makethingshappy/IoTextra-Digital/Input/v.3.02/media/01_-_IoTextra_Input_3D_view.png

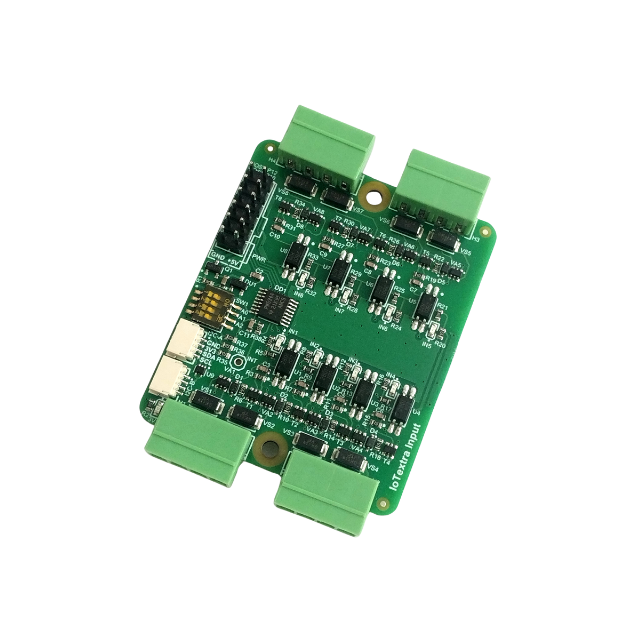
Input/v.3.02/media/01_-_IoTextra_Input_3D_view.png
