makethingshappy/IoTextra-Digital/Input/v.3.02/media/02_-_IoTextra_Input_with_and_without_Qwiic_connector.png

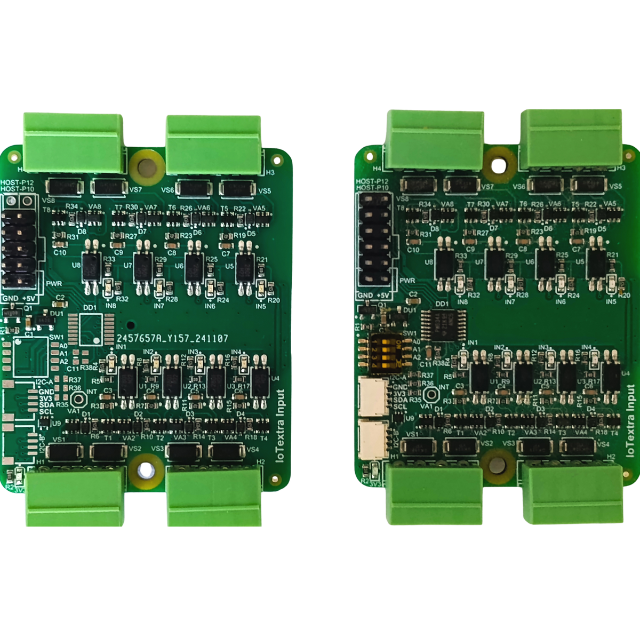
Input/v.3.02/media/02_-_IoTextra_Input_with_and_without_Qwiic_connector.png
