makethingshappy/IoTextra-Digital/Input/v.3.02/media/03_-_IoTextra_Input_TOP_view.png

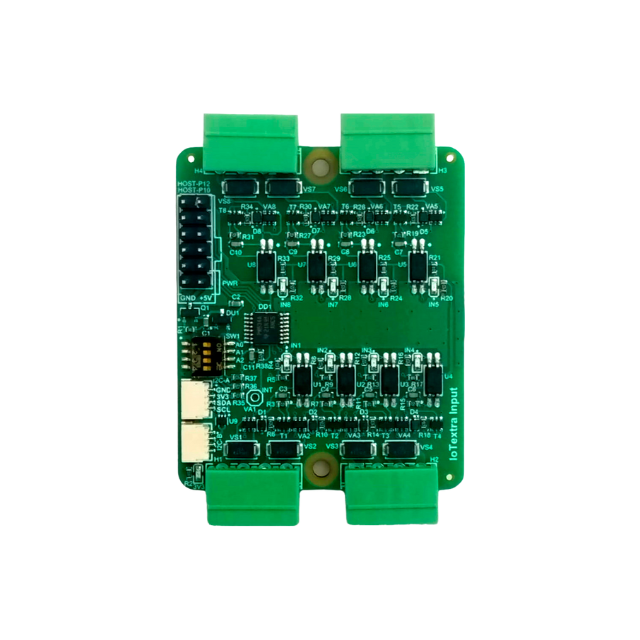
Input/v.3.02/media/03_-_IoTextra_Input_TOP_view.png
