makethingshappy/IoTextra-Digital/Input/v.3.02/media/04_-_IoTextra_Input_BOTTOM_view.png

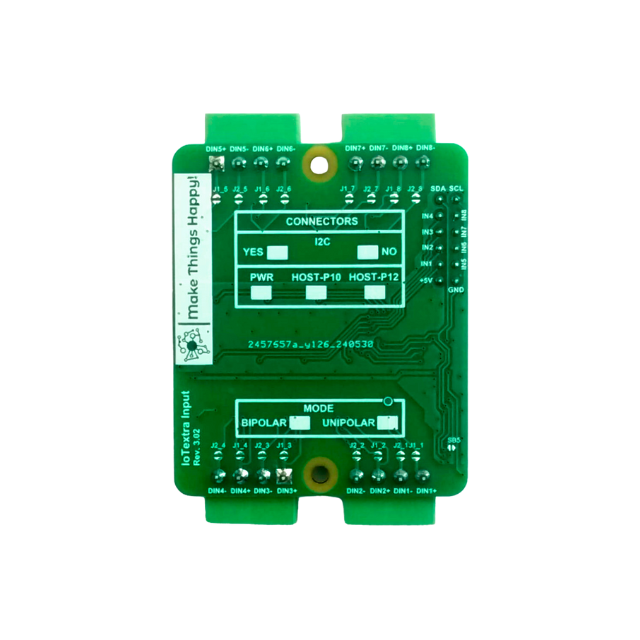
Input/v.3.02/media/04_-_IoTextra_Input_BOTTOM_view.png
