makethingshappy/IoTextra-Digital/Input/v.3.02/media/05_-_IoTextra_Input_HOST_connector_pinout.png

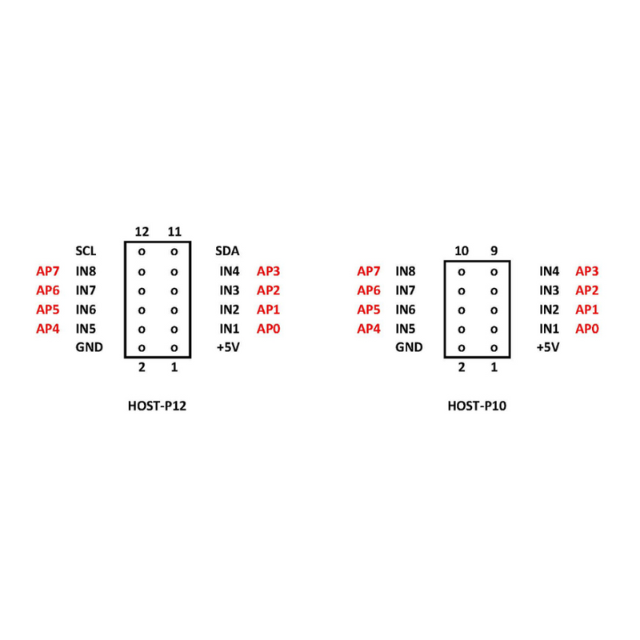
Input/v.3.02/media/05_-_IoTextra_Input_HOST_connector_pinout.png
