makethingshappy/IoTextra-Digital/Input/v.3.02/media/06_-_IoTsmart_RP2040_and_IoTextra_Input.png

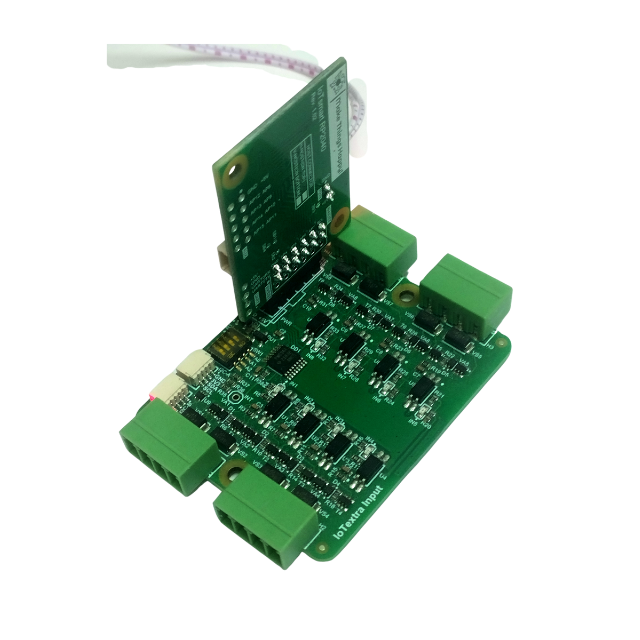
Input/v.3.02/media/06_-_IoTsmart_RP2040_and_IoTextra_Input.png
