makethingshappy/IoTextra-Digital/Input/v.3.02/media/07_-_IoTsmart_RP2350_and_IoTextra_Input.png

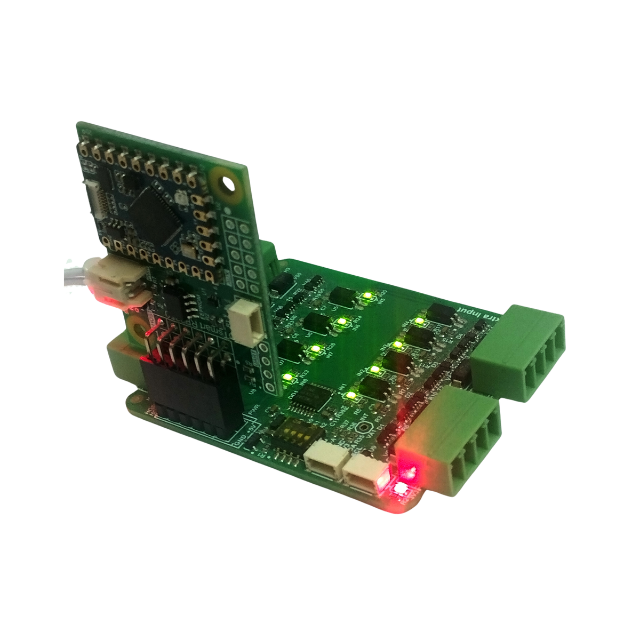
Input/v.3.02/media/07_-_IoTsmart_RP2350_and_IoTextra_Input.png
