makethingshappy/IoTextra-Digital/Input/v.3.02/media/12_-_IoTbase_PICO_and_IoTextra_Input_with_Raspberry_PICO2.png

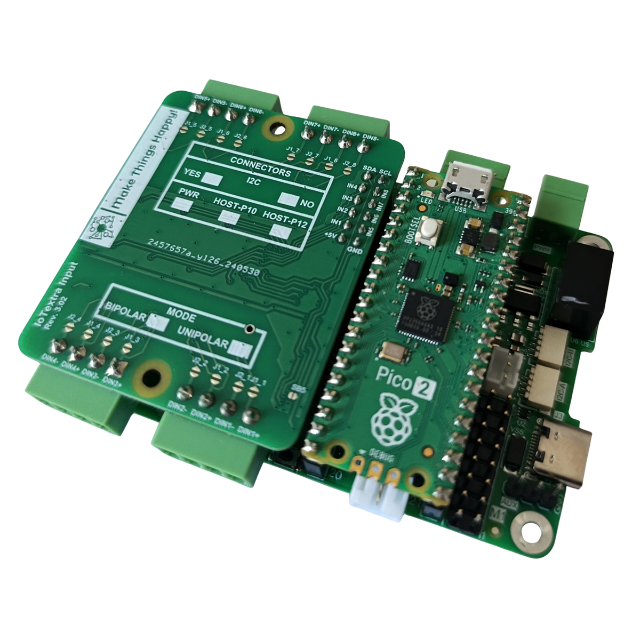
Input/v.3.02/media/12_-_IoTbase_PICO_and_IoTextra_Input_with_Raspberry_PICO2.png
