makethingshappy/IoTextra-Digital/Input/v.3.02/media/13_-_IoTextra_Input_and_IoTbase_PICO_with_RP2040_Plus.png

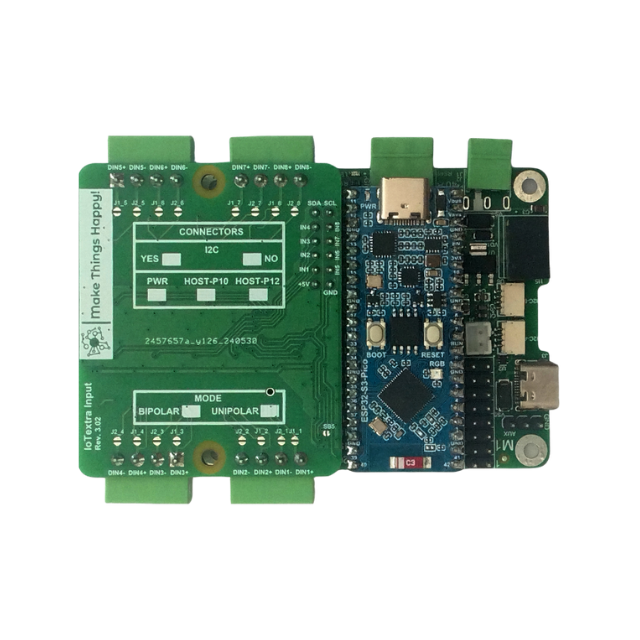
Input/v.3.02/media/13_-_IoTextra_Input_and_IoTbase_PICO_with_RP2040_Plus.png
