makethingshappy/IoTextra-Digital/Input/v.3.02/media/15_-_IoTextra_Input_and_Raspberry_Pi_Zero.png

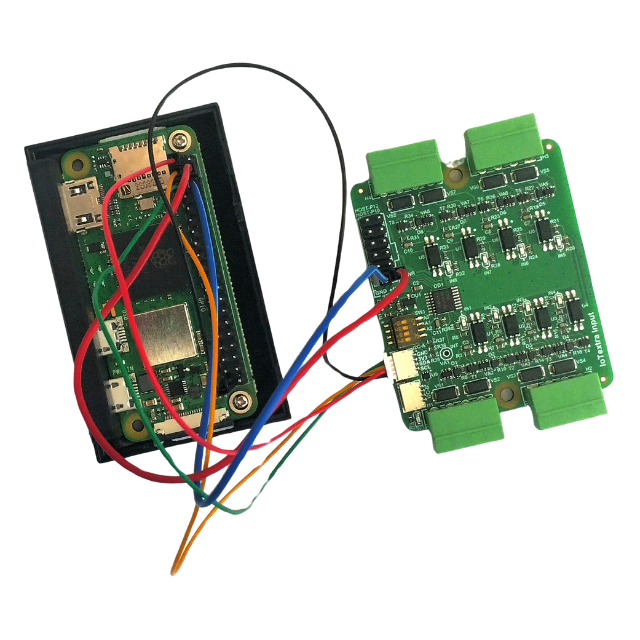
Input/v.3.02/media/15_-_IoTextra_Input_and_Raspberry_Pi_Zero.png
