makethingshappy/IoTextra-Digital/Input/v.3.02/media/16_-_IoTextra_Input_and_Feather_Adaptor_with_Proton2.png

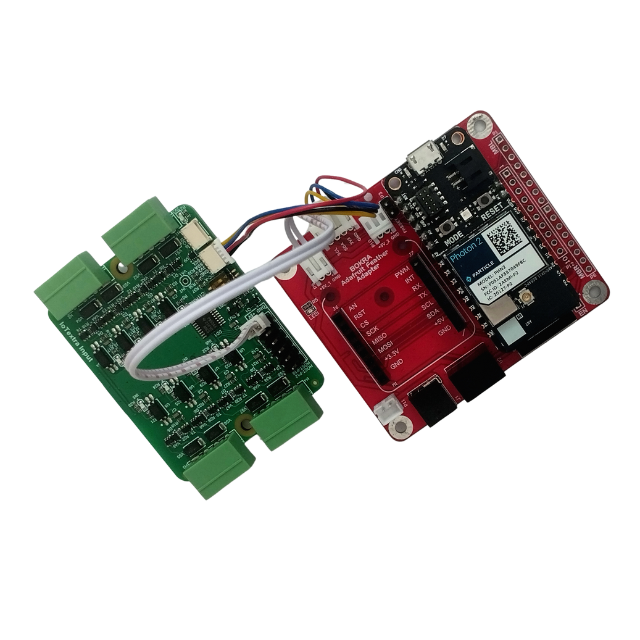
Input/v.3.02/media/16_-_IoTextra_Input_and_Feather_Adaptor_with_Proton2.png
