makethingshappy/IoTextra-Digital/MOSFET2/v.3.02/media/01 - IoTextra MOSFET2 and IoTsmart ESP32-S3 .png

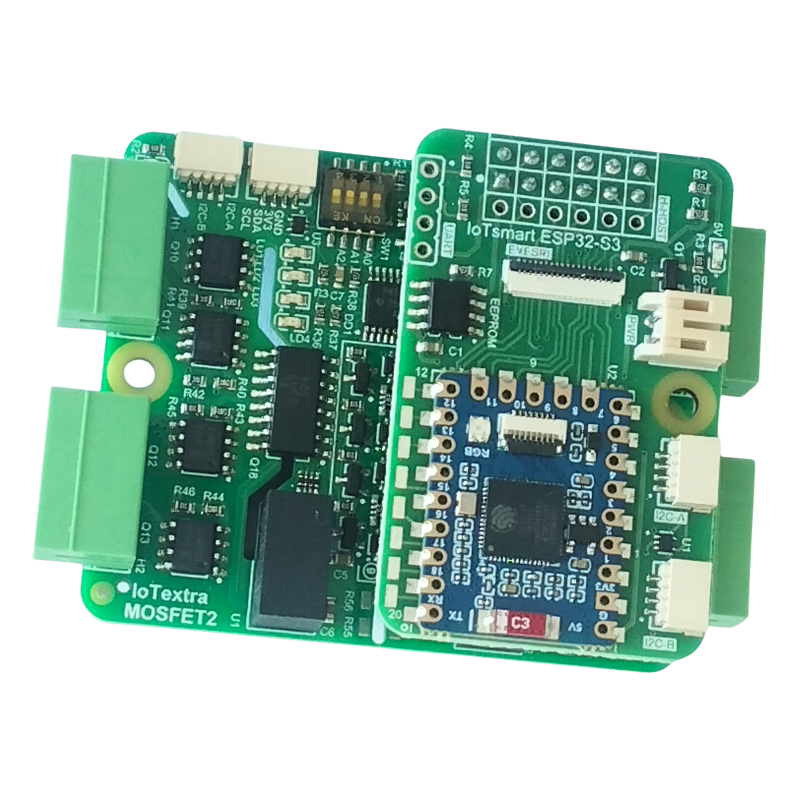
MOSFET2/v.3.02/media/01 - IoTextra MOSFET2 and IoTsmart ESP32-S3 .png
