makethingshappy/IoTextra-Digital/MOSFET2/v.3.02/media/02 - IoTextra MOSFET2 TOP view.png

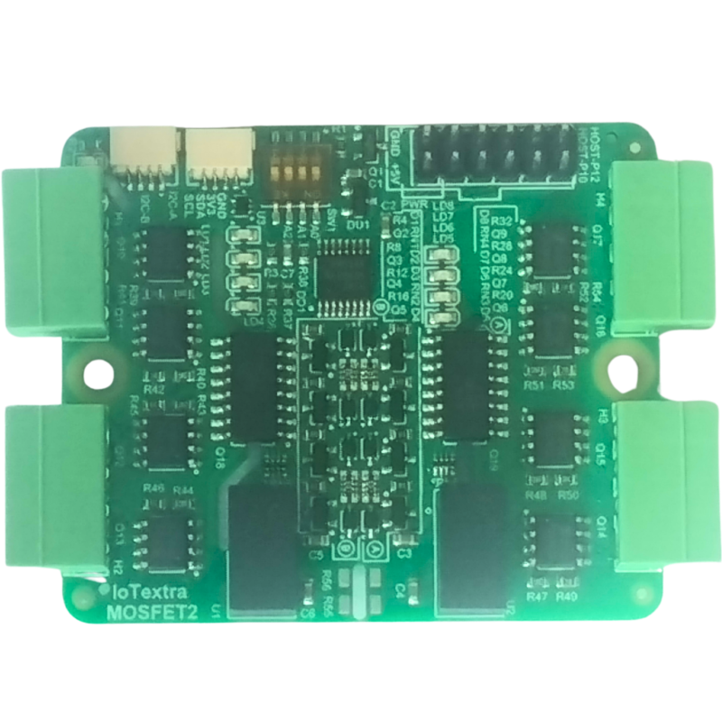
MOSFET2/v.3.02/media/02 - IoTextra MOSFET2 TOP view.png
