makethingshappy/IoTextra-Digital/MOSFET2/v.3.02/media/05 - IoTextra MOSFET2 and IoTsmart RP2350A.png

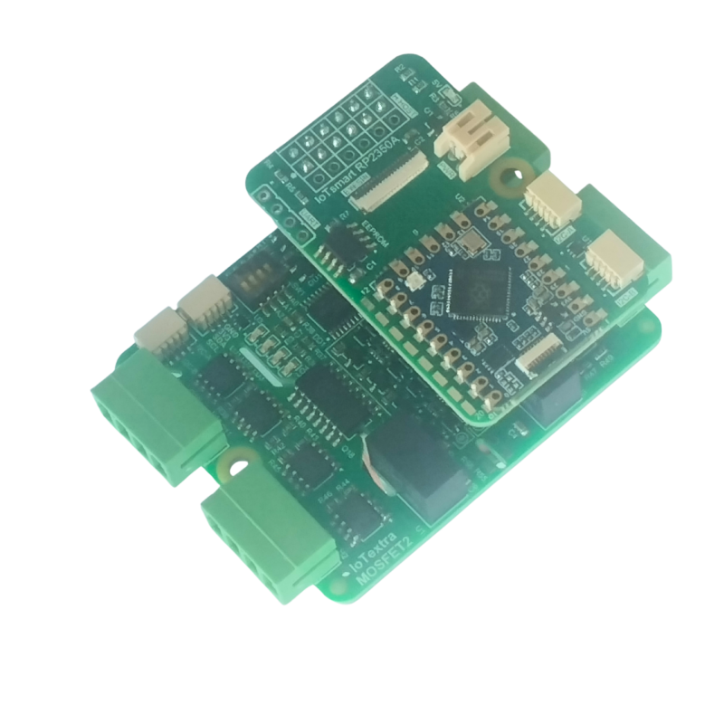
MOSFET2/v.3.02/media/05 - IoTextra MOSFET2 and IoTsmart RP2350A.png
