makethingshappy/IoTextra-Digital/MOSFET2/v.3.02/media/07 - IoTextra MOSFET2 and IoTsmart XIAO with XIAO ESP32-C6.png

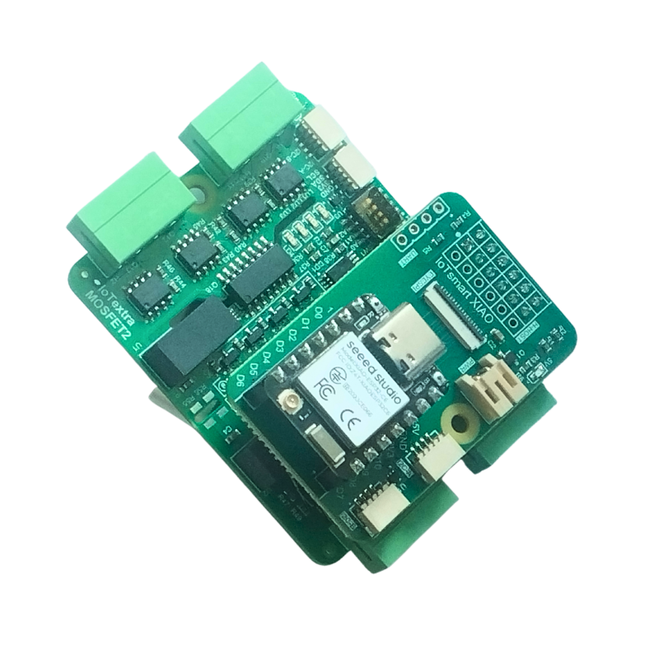
MOSFET2/v.3.02/media/07 - IoTextra MOSFET2 and IoTsmart XIAO with XIAO ESP32-C6.png
