makethingshappy/IoTextra-Digital/MOSFET2/v.3.02/media/08 - IoTextra MOSFET2 and IoTbase Feather with Proton2.png

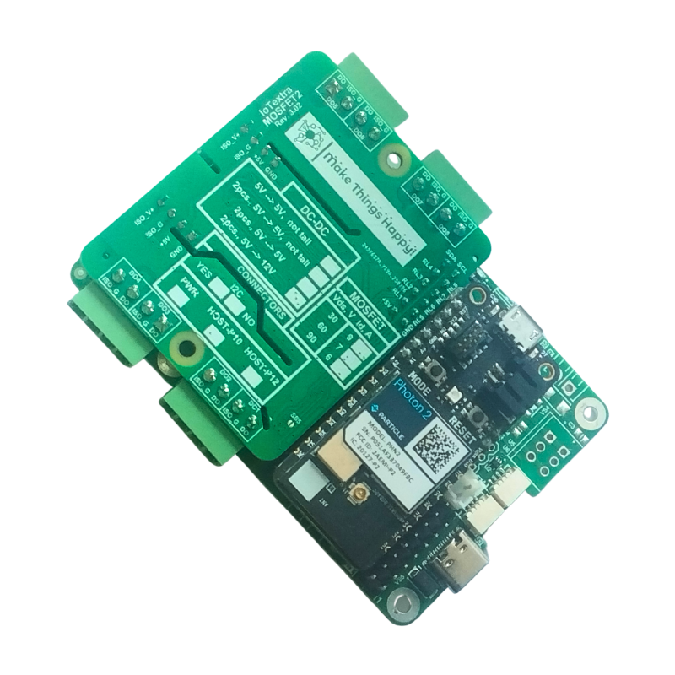
MOSFET2/v.3.02/media/08 - IoTextra MOSFET2 and IoTbase Feather with Proton2.png
