makethingshappy/IoTextra-Digital/Octal3/v.3.02/media/01 - IoTextra Octal3 - 3D view.png

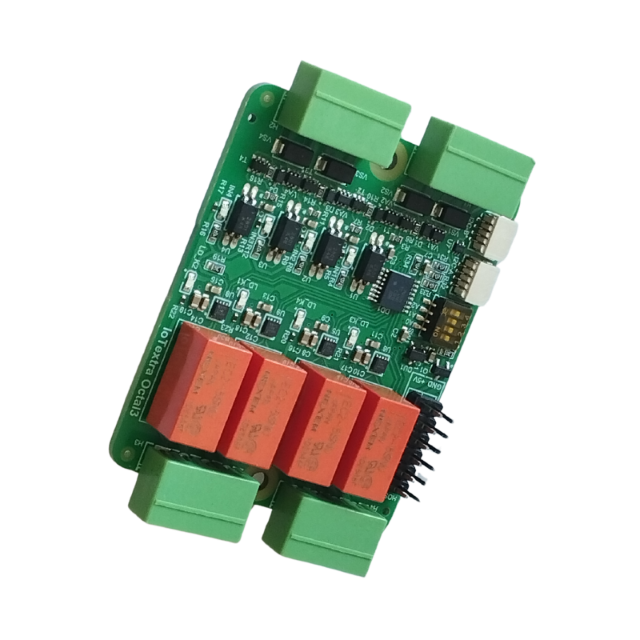
Octal3/v.3.02/media/01 - IoTextra Octal3 - 3D view.png
