makethingshappy/IoTextra-Digital/Octal3/v.3.02/media/02 - IoTextra Octal3 - TOP.png

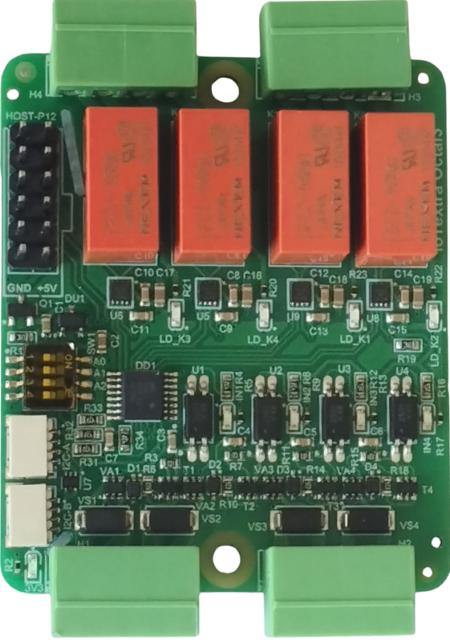
Octal3/v.3.02/media/02 - IoTextra Octal3 - TOP.png
