makethingshappy/IoTextra-Digital/Octal3/v.3.02/media/03 - IoTextra Octal3 - BOTTOM view.png

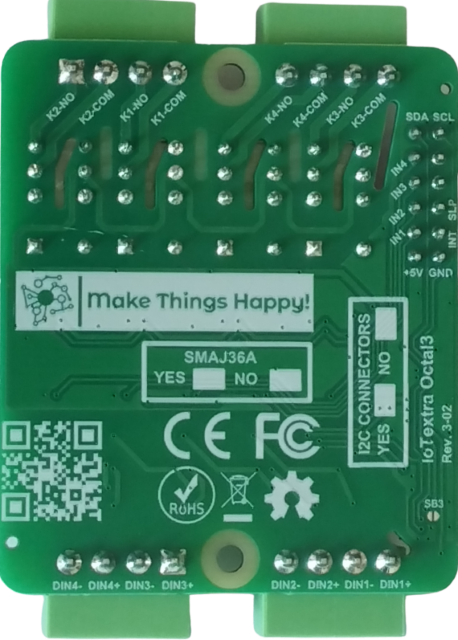
Octal3/v.3.02/media/03 - IoTextra Octal3 - BOTTOM view.png
