makethingshappy/IoTextra-Digital/Octal3/v.3.02/media/04 - HOST.jpg

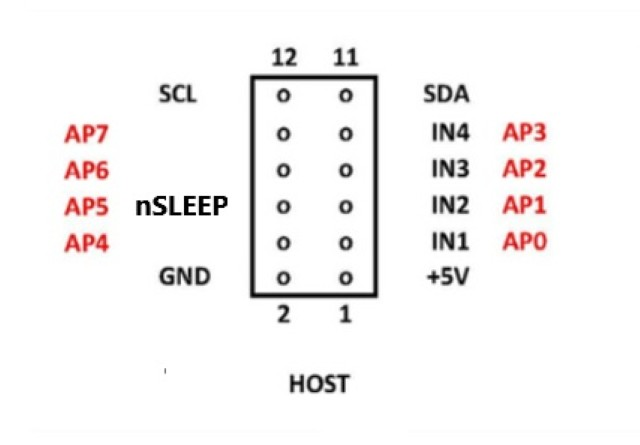
Octal3/v.3.02/media/04 - HOST.jpg
