makethingshappy/IoTextra-Digital/Octal3/v.3.02/media/05 - IoTextra Octal3 and IoTsmart RP2040 .png

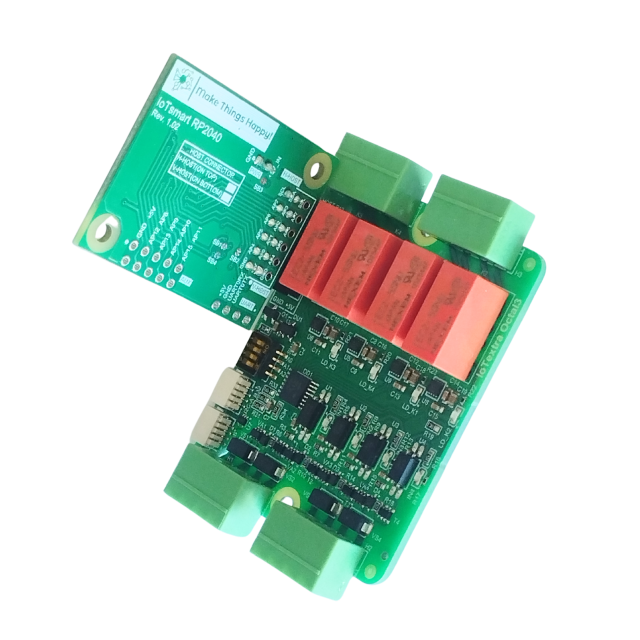
Octal3/v.3.02/media/05 - IoTextra Octal3 and IoTsmart RP2040 .png
