makethingshappy/IoTextra-Digital/Octal3/v.3.02/media/06 - IoTextra Octal3 and IoTsmart RP2350A 2-01 .png

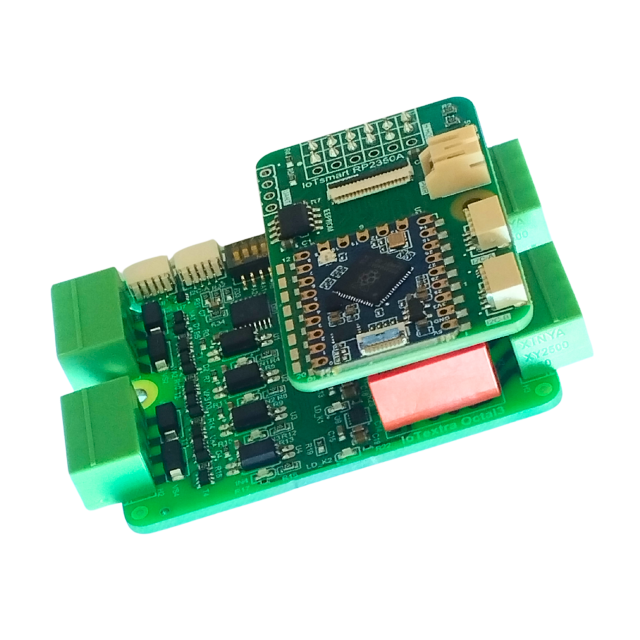
Octal3/v.3.02/media/06 - IoTextra Octal3 and IoTsmart RP2350A 2-01 .png
