makethingshappy/IoTextra-Digital/Octal3/v.3.02/media/07 - IoTextra Octal3 and IoTsmart RP2350 1-02 .png

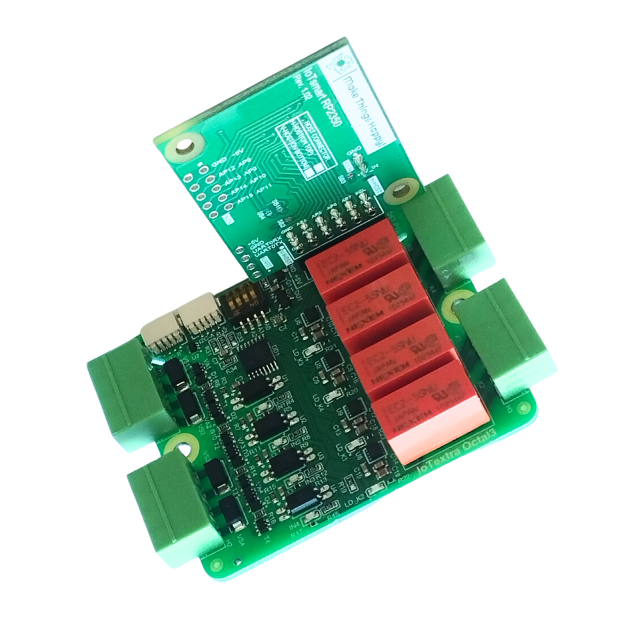
Octal3/v.3.02/media/07 - IoTextra Octal3 and IoTsmart RP2350 1-02 .png
