makethingshappy/IoTextra-Digital/Octal3/v.3.02/media/08 - IoTextra Octal3 and IoTsmart ESP32-S3 2-01 - 1.png

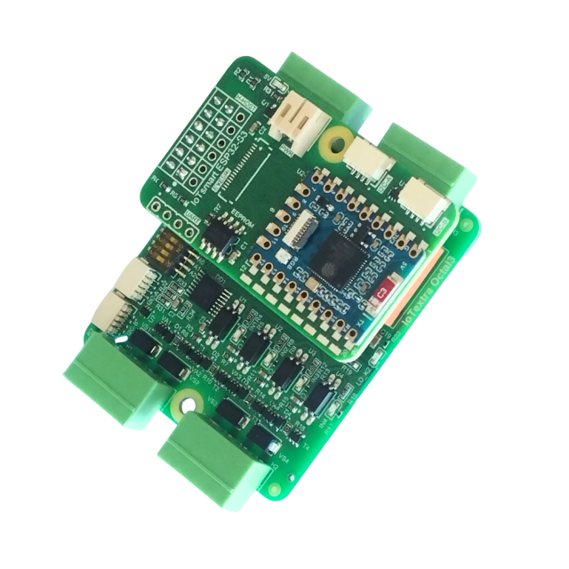
Octal3/v.3.02/media/08 - IoTextra Octal3 and IoTsmart ESP32-S3 2-01 - 1.png
