makethingshappy/IoTextra-Digital/Octal3/v.3.02/media/10 - IoTextra Octal3 and IoTsmart ESP32-S3 1-02.png

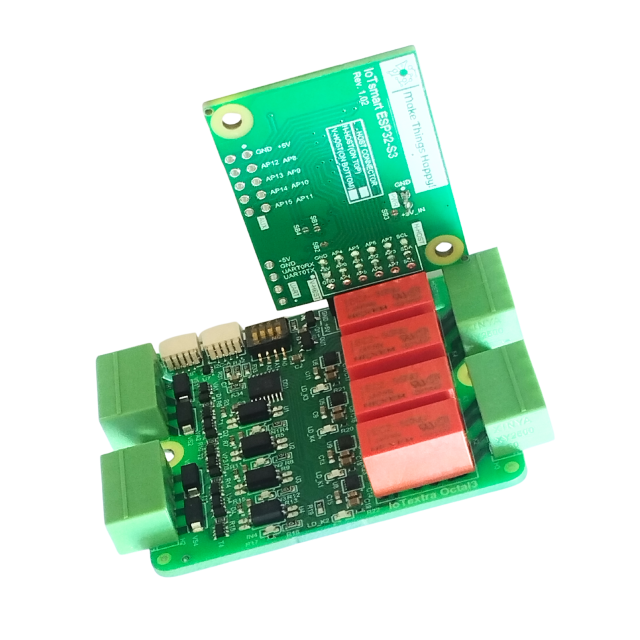
Octal3/v.3.02/media/10 - IoTextra Octal3 and IoTsmart ESP32-S3 1-02.png
