makethingshappy/IoTextra-Digital/Octal/v.3.04/media/02 - IoTextra Octal TOP view.png

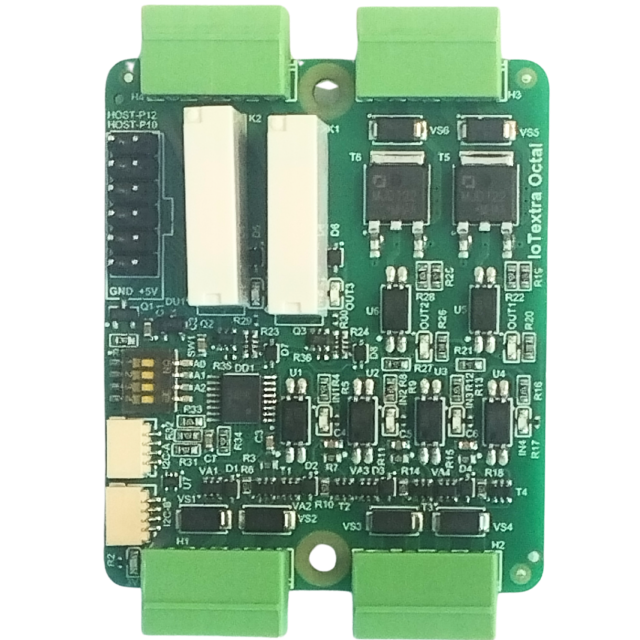
Octal/v.3.04/media/02 - IoTextra Octal TOP view.png
