makethingshappy/IoTextra-Digital/Octal/v.3.04/media/03 - IoTextra Octal BOTTOM view.png

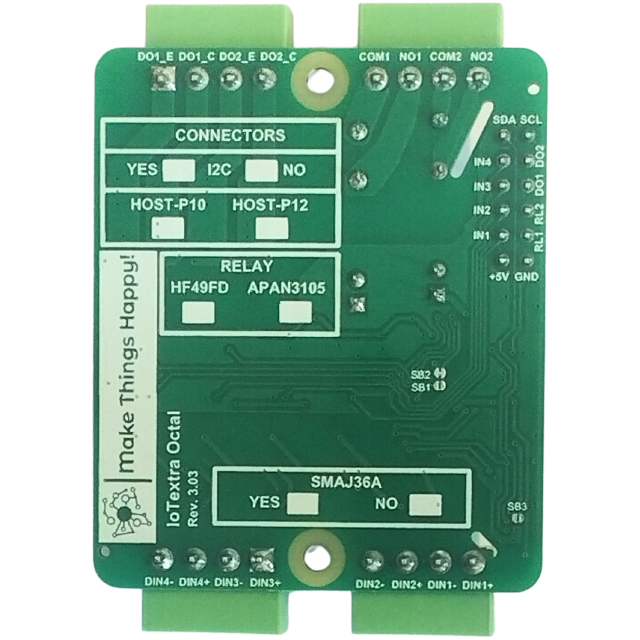
Octal/v.3.04/media/03 - IoTextra Octal BOTTOM view.png
