makethingshappy/IoTextra-Digital/Octal/v.3.04/media/05 - IoTextra Octal and IoTsmart RP2040 1-02.png

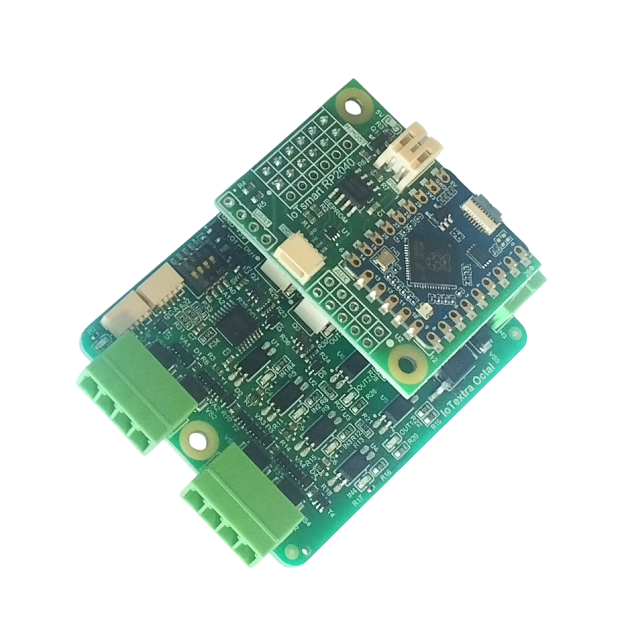
Octal/v.3.04/media/05 - IoTextra Octal and IoTsmart RP2040 1-02.png
