makethingshappy/IoTextra-Digital/Octal/v.3.04/media/06 - IoTextra Octal and IoTsmart RP2350 1-02 - 1.png

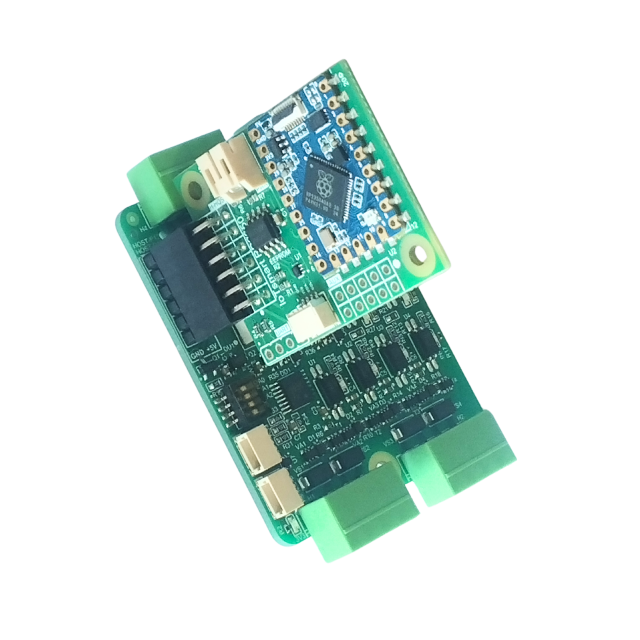
Octal/v.3.04/media/06 - IoTextra Octal and IoTsmart RP2350 1-02 - 1.png
