makethingshappy/IoTextra-Digital/Octal/v.3.04/media/07 - IoTextra Octal and IoTsmart RP2350 1-02 - 2.png

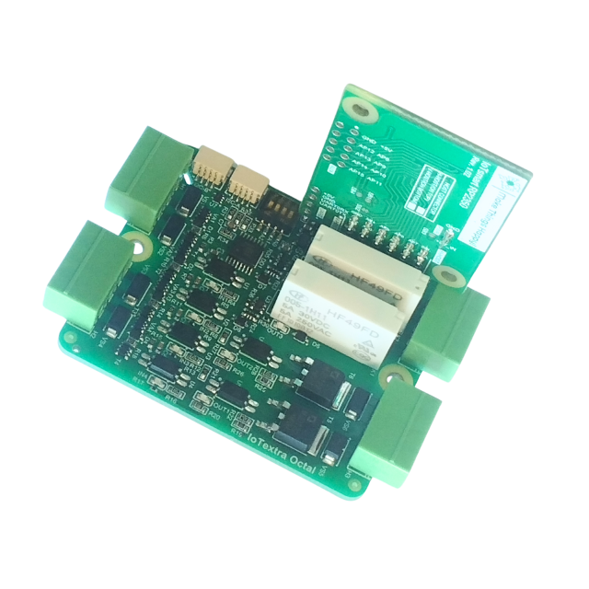
Octal/v.3.04/media/07 - IoTextra Octal and IoTsmart RP2350 1-02 - 2.png
