makethingshappy/IoTextra-Digital/Octal/v.3.04/media/08 - IoTextra Octal and IoTsmart RP2350 2-01 A.png

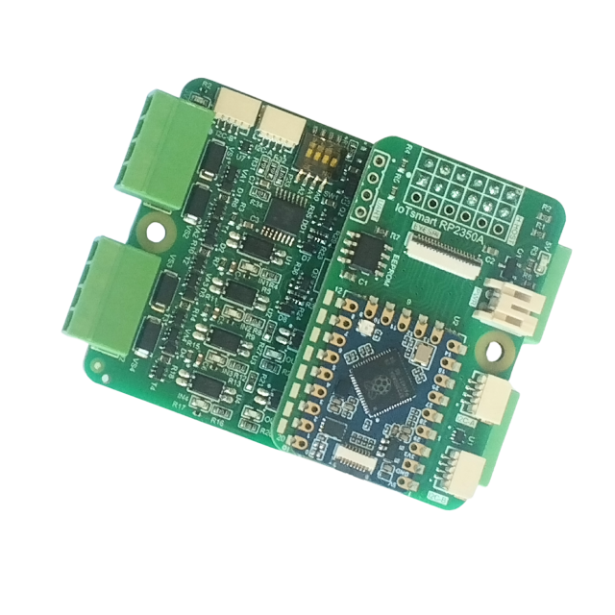
Octal/v.3.04/media/08 - IoTextra Octal and IoTsmart RP2350 2-01 A.png
