makethingshappy/IoTextra-Digital/Octal/v.3.04/media/10 - IoTextra Octal and IoTbase PICO with PICO2.png

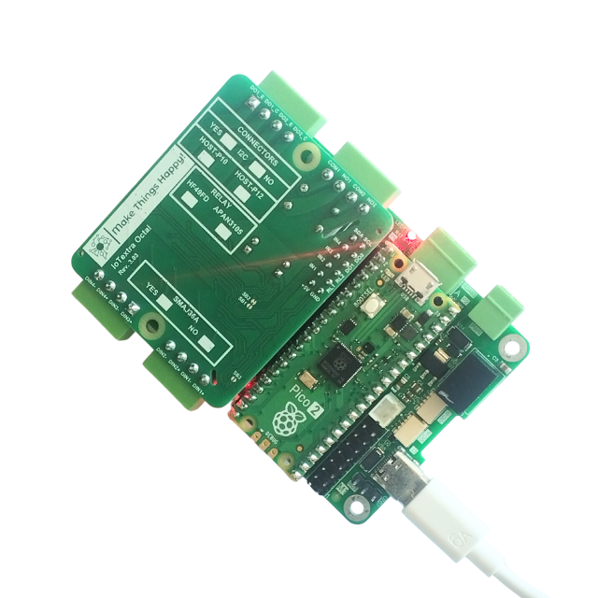
Octal/v.3.04/media/10 - IoTextra Octal and IoTbase PICO with PICO2.png
