makethingshappy/IoTextra-Digital/Octal/v.3.04/media/11 - IoTextra Octal and IoTbase PICO with Waveshare ESP32-S3-Pico.png

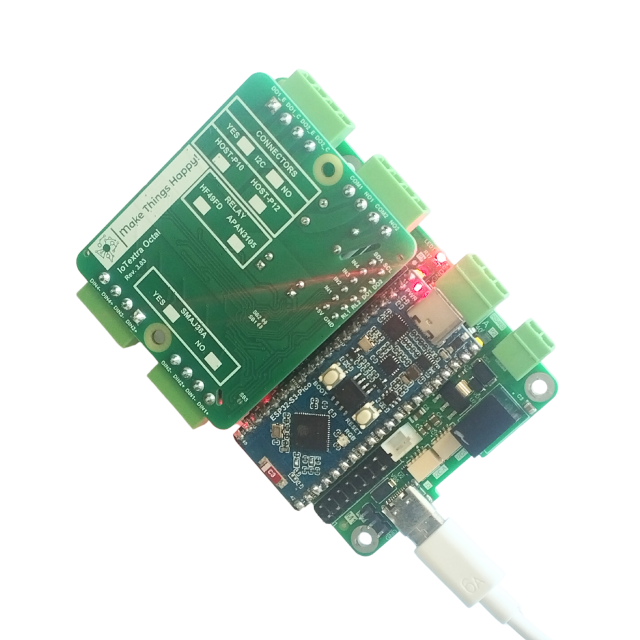
Octal/v.3.04/media/11 - IoTextra Octal and IoTbase PICO with Waveshare ESP32-S3-Pico.png
