makethingshappy/IoTextra-Digital/Octal/v.3.04/media/12 - IoTextra Octal and IoTbase NANO with Waveshare ESP32-S3-NANO.png

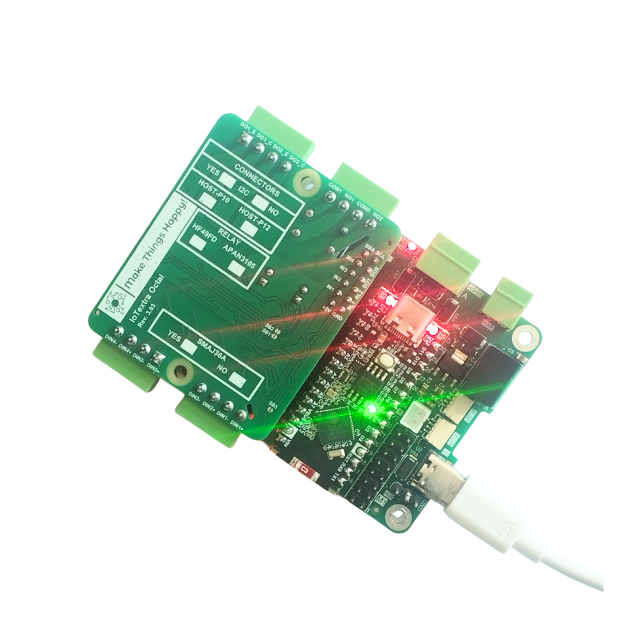
Octal/v.3.04/media/12 - IoTextra Octal and IoTbase NANO with Waveshare ESP32-S3-NANO.png
