makethingshappy/IoTextra-Digital/Relay2/v3.02/media/02_-_IoTextra_Relay2_with_and_without_Qwiic_connector.png

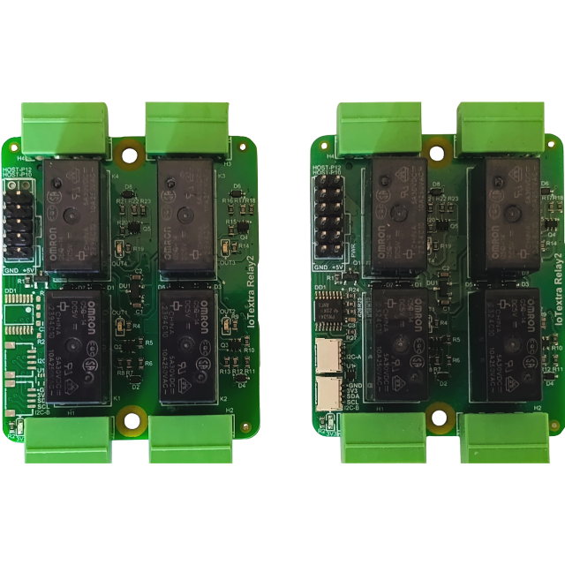
Relay2/v3.02/media/02_-_IoTextra_Relay2_with_and_without_Qwiic_connector.png
