makethingshappy/IoTextra-Digital/Relay2/v3.02/media/04_-_IoTextra_Relay2_BOTTOM_view.png

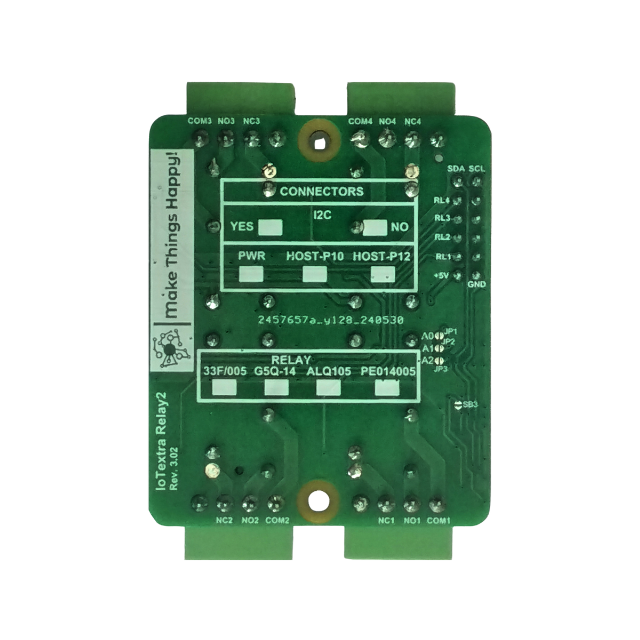
Relay2/v3.02/media/04_-_IoTextra_Relay2_BOTTOM_view.png
