makethingshappy/IoTextra-Digital/Relay2/v3.02/media/06_-_IoTsmart_RP2040_and_IoTextra_Relay2_-_1.png

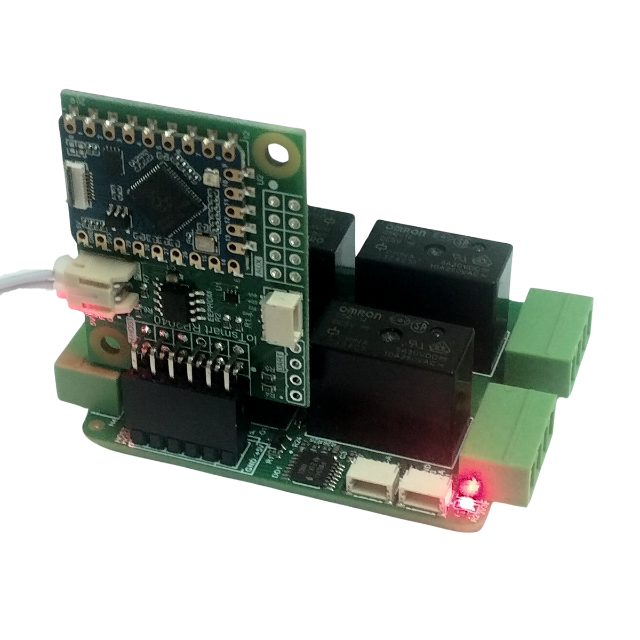
Relay2/v3.02/media/06_-_IoTsmart_RP2040_and_IoTextra_Relay2_-_1.png
