makethingshappy/IoTextra-Digital/Relay2/v3.02/media/11_-_IoTextra_Relay2_and_Raspberry_Pi_Zero.png

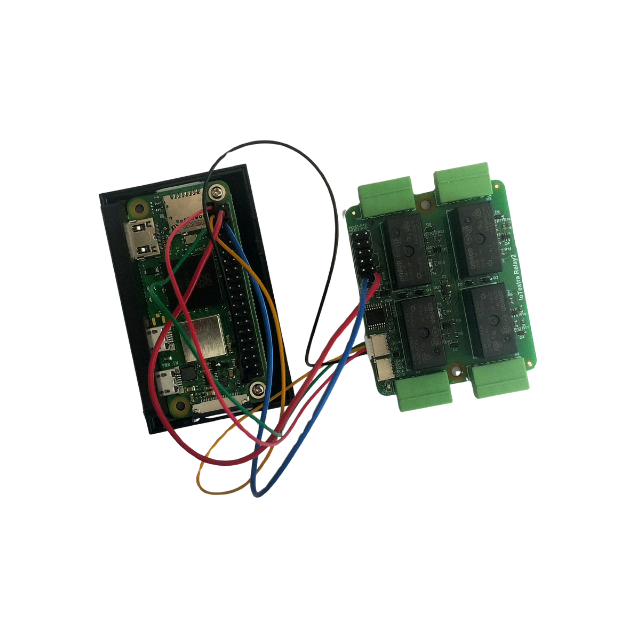
Relay2/v3.02/media/11_-_IoTextra_Relay2_and_Raspberry_Pi_Zero.png
