makethingshappy/IoTextra-Digital/Relay2/v3.02/media/12_-_IoTexra_Relay2_and_Feather_Adaptor_with_Proton2.png

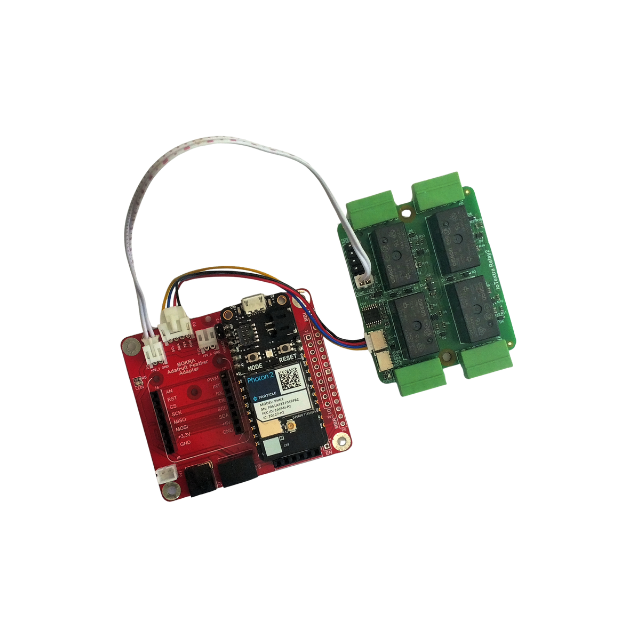
Relay2/v3.02/media/12_-_IoTexra_Relay2_and_Feather_Adaptor_with_Proton2.png
