makethingshappy/IoTextra-Digital/SSR Small/v.3.02/media/03_-_IoTextra_SSR_Small_TOP_view.png

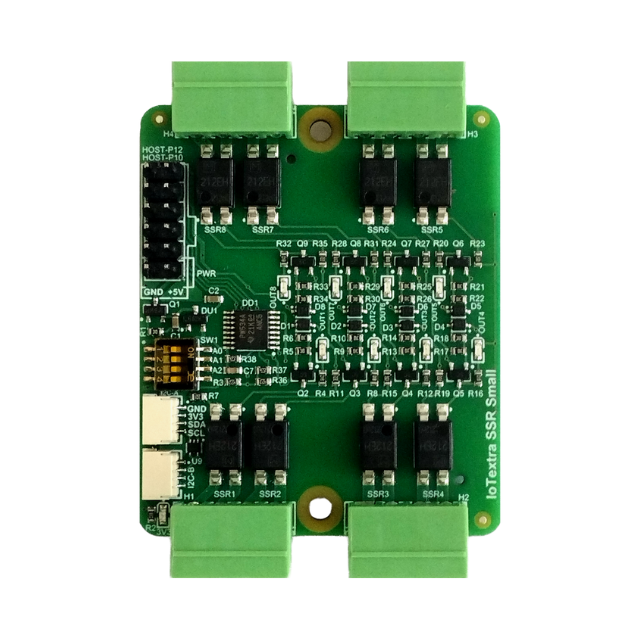
SSR Small/v.3.02/media/03_-_IoTextra_SSR_Small_TOP_view.png
