makethingshappy/IoTextra-Digital/SSR Small/v.3.02/media/04_-_IoTextra_SSR_Small_BOTTOM_view.png

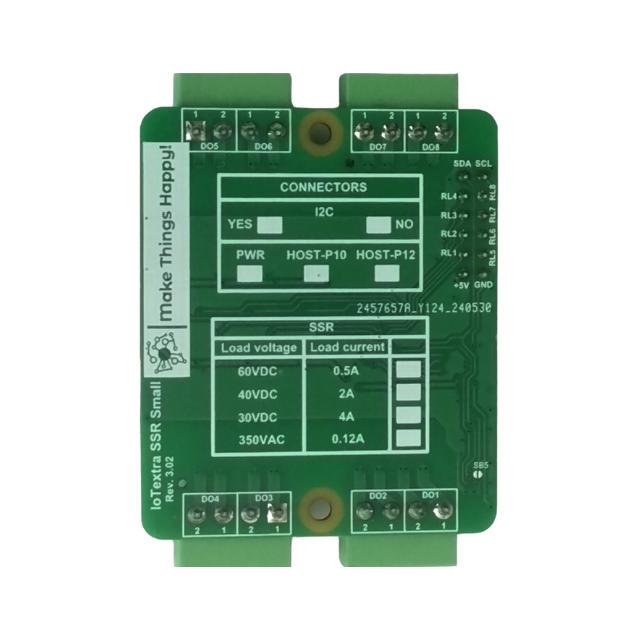
SSR Small/v.3.02/media/04_-_IoTextra_SSR_Small_BOTTOM_view.png
