makethingshappy/IoTextra-Digital/SSR Small/v.3.02/media/06_-_IoTsmart_RP2040_and_IoTextra_SSR_Small.png

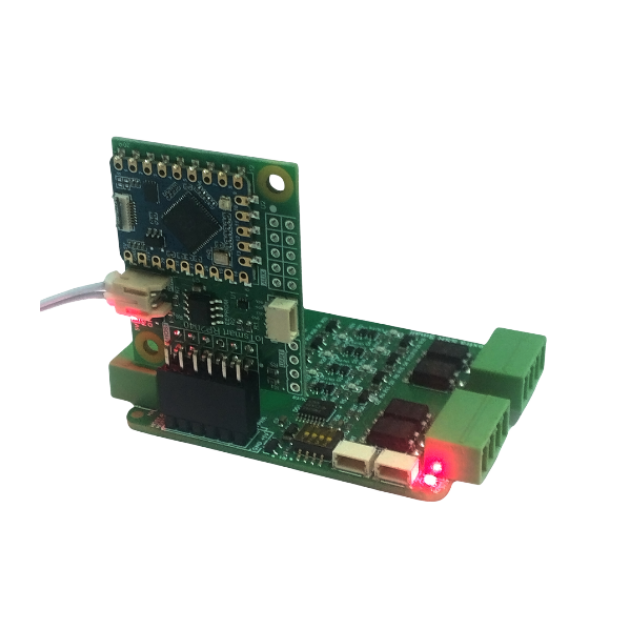
SSR Small/v.3.02/media/06_-_IoTsmart_RP2040_and_IoTextra_SSR_Small.png
