makethingshappy/IoTextra-Digital/SSR Small/v.3.02/media/07-_IoTsmart_RP2350_and_IoTextra_SSR_Small.png

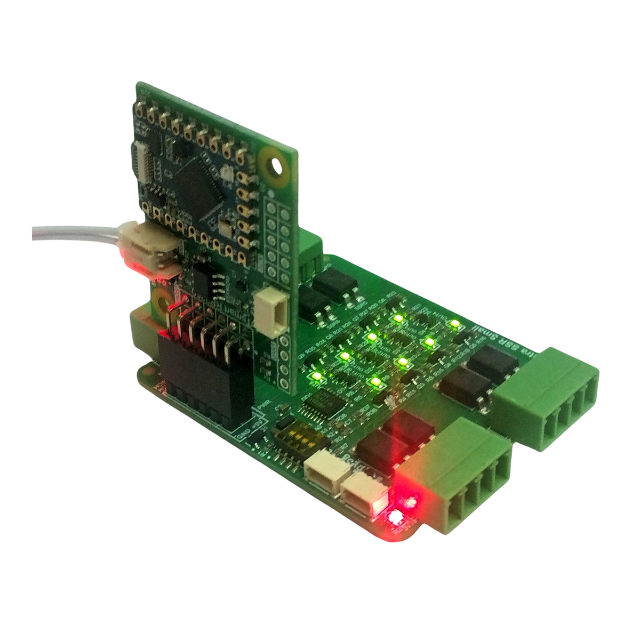
SSR Small/v.3.02/media/07-_IoTsmart_RP2350_and_IoTextra_SSR_Small.png
