makethingshappy/IoTextra-Digital/SSR Small/v.3.02/media/13_-_IoTbase_NANO_and_IoTextra_SSR_Small_with_ESP32-S3-Nano_Development_Board.png

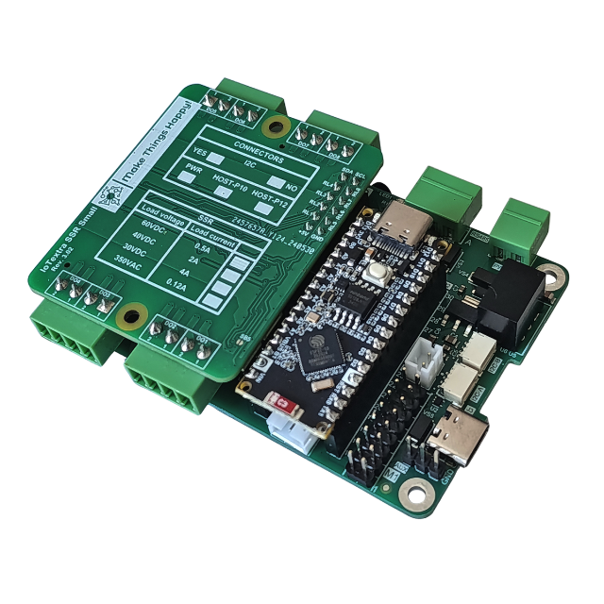
SSR Small/v.3.02/media/13_-_IoTbase_NANO_and_IoTextra_SSR_Small_with_ESP32-S3-Nano_Development_Board.png
